thechakmv/Lovers-Rock/images/final_trans_sim.png

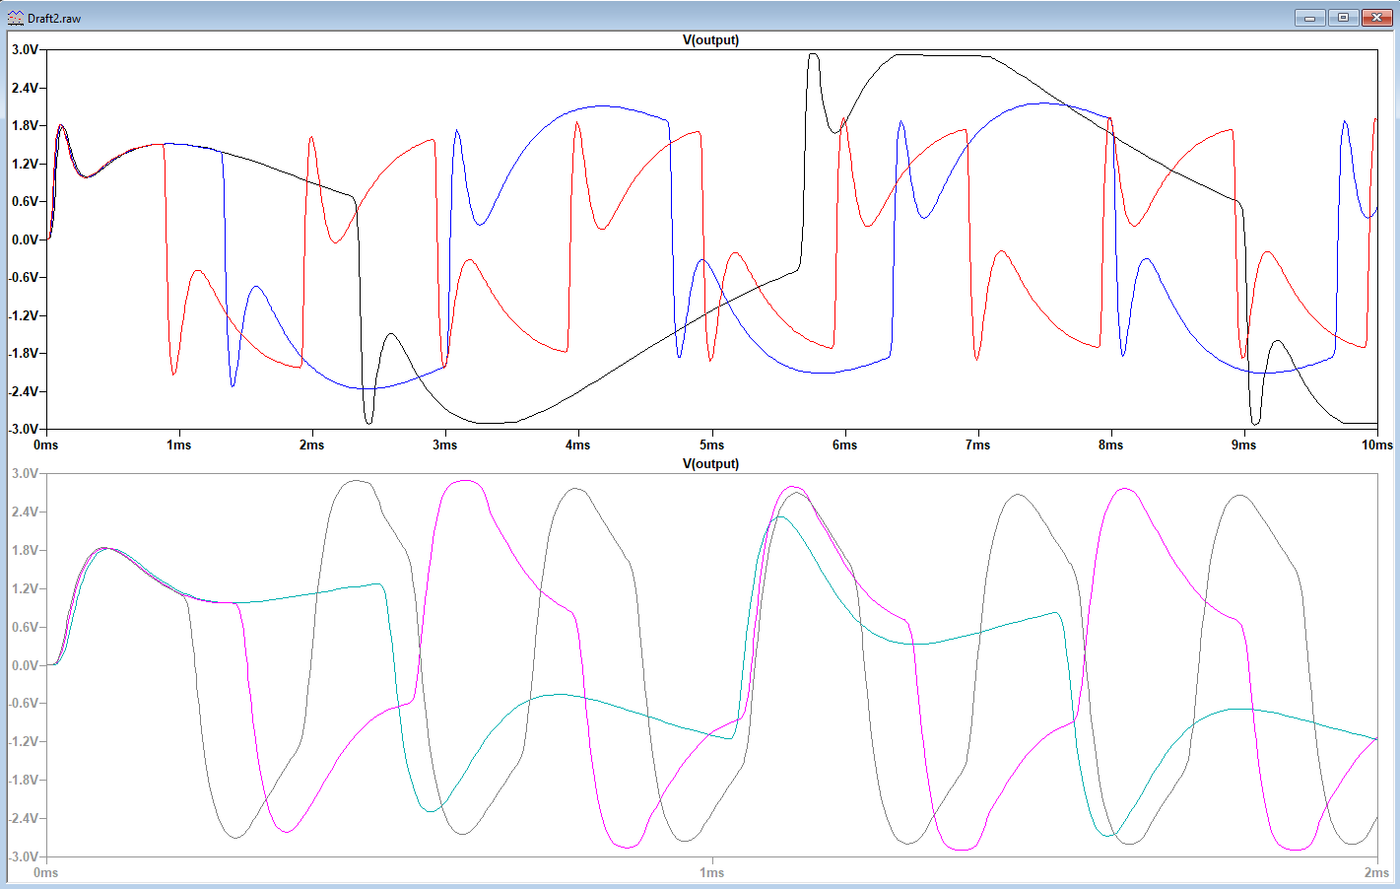
images/final_trans_sim.png
