thechakmv/Lovers-Rock/images/od_ds_bode.png

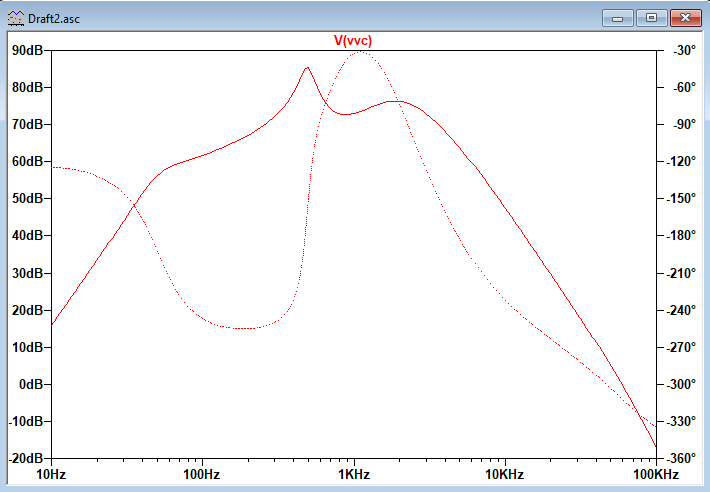
images/od_ds_bode.png
