thechakmv/Lovers-Rock/ltspice/Draft2.asc

C1: cap; 100n
C2: cap
C3: cap; 1µ
C4: cap; 4.7n
C5: cap; 100n
C6: cap; 1µF
C7: cap; 47nF
C8: cap; 330pF
C9: cap; 1µF
C10: cap; 51pF
C11: cap; 47µ
C12: cap; 4.7n
C13: cap; 100n
C14: cap
C15: cap
C17: cap; 100µF
Cin1: cap; 100nf
D1: diode; 1N4148
D2: diode; 1N4148
D3: diode; 1N4148
D4: diode; 1N4148
D5: schottky
L1: ind
Pot1: res; 250K
Pot2: res; 500K
R1: res; 1Meg
R2: res; 10K
R3: res; 1Meg
R4: res; 100
R5: res; 10K
R6: res; 1Meg
R7: res; 10K
R8: res; 100
R9: res; 10K
R10: res; 10K
R11: res; 1Meg
R12: res; 10K
R13: res; 100K
R14: res
R15: res; 470
R16: res; 1Meg
R17: res; 1K
R18: res; 10K
R19: res; 10K
R20: res
R21: res; 1K
R22: res; 10K
R23: res; 1Meg
R24: res; 0
R25: res
R28: res; 1Meg
Rout1: res; 470
Rpull1: res; 1Meg
U1: OP07
U2: OP07
U3: OP07
U4: OP07
U5: OP07
U6: OP07
U7: opamp
V1: signal; SINE(0 50m {Freq}); AC 1
V4: voltage; 9V
Named nets: 0, Vref, Vpow, Vs, Vin, Vds, Output, Vvc, Vod, out
Overdrive Stage
Distortion Stage
Post Distortion Filtering
;ac dec 50 10 100K
Power / Input Stage
Volume Control
.param Freq=300
.step param Freq LIST 150 300 500 1K 2K 3k
.tran 10m
=
